mozilla/project_haiku.iot/Bluetooth/HC-05-Bluetooth-Module/Communicate_Master_Slave/BL-Slave-Pair/BL-Slave-Pair.ino

/*
* Sketch: Arduino2Arduino_SLAVE_01
* By Martyn Currey
* 08.04.2016
* Written in Arduino IDE 1.6.5
*
* Receive commands through a serial connection and turn a LED on or OFF
* There is no error checking and this sketch receives only
* Commands should be contained within the start and end markers < and >
*
* D8 - software serial RX
* D9 - software serial TX
* D3 - LED
*
*/
 
// AltSoftSerial uses D9 for TX and D8 for RX. While using AltSoftSerial D10 cannot be used for PWM.
// Remember to use a voltage divider on the Arduino TX pin / Bluetooth RX pin
// Download AltSoftSerial from https://www.pjrc.com/teensy/td_libs_AltSoftSerial.html
 
#include <AltSoftSerial.h>
AltSoftSerial BTserial; 
 
// Change DEBUG to true to output debug information to the serial monitor
boolean DEBUG = true;
 
 
// Variables used for incoming data
const byte maxDataLength = 20;          // maxDataLength is the maximum length allowed for received data.
char receivedChars[maxDataLength+1] ;
boolean newData = false;               // newData is used to determine if there is a new command
 
void setup()  
{
    // LED on pin 3
    pinMode(3, OUTPUT); 
    digitalWrite(3,LOW);
 
 
    if (DEBUG)
    {
        // open serial communication for debugging and show the sketch name and the date compiled
        Serial.begin(9600);
        Serial.println(__FILE__);
        Serial.println(__DATE__);
        Serial.println(" ");
    }
 
    //  open software serial connection to the Bluetooth module.
    BTserial.begin(9600); 
    if (DEBUG)  {   Serial.println(F("AltSoftSerial started at 9600"));     }
 
    newData = false;
 
}
 
void loop()  
{
         recvWithStartEndMarkers();                // check to see if we have received any new commands
         if (newData)  {   processCommand();  }    // if we have a new command do something
}
 
 
void processCommand()
{
    newData = false;
    if (DEBUG)  {   Serial.print("recieved data = ");  Serial.println(receivedChars);         }
 
    if      (strcmp ("LEDON",receivedChars) == 0)  { digitalWrite(3,HIGH);   }
    else if (strcmp ("LEDOFF",receivedChars) == 0) { digitalWrite(3,LOW);    }
}
 
// function recvWithStartEndMarkers by Robin2 of the Arduino forums
// See  http://forum.arduino.cc/index.php?topic=288234.0
void recvWithStartEndMarkers() 
{
     static boolean recvInProgress = false;
     static byte ndx = 0;
     char startMarker = '<';
     char endMarker = '>';
 
     if (BTserial.available() > 0) 
     {
          char rc = BTserial.read();
          if (recvInProgress == true) 
          {
               if (rc != endMarker) 
               {
                    if (ndx < maxDataLength) { receivedChars[ndx] = rc; ndx++;  }
               }
               else 
               {
                     receivedChars[ndx] = '\0'; // terminate the string
                     recvInProgress = false;
                     ndx = 0;
                     newData = true;
               }
          }
          else if (rc == startMarker) { recvInProgress = true; }
     }
 
}
