mozilla/project_haiku.iot/Bluetooth/HC-05-Bluetooth-Module/Setup_Master_Slave/BL-Master-Pair-SoftwareSerial-AT-Mode/BL-Master-Pair-SoftwareSerial-AT-Mode.ino

// Basic Bluetooth sketch HC-05_02_38400
// Connect the HC-05 module and communicate using the serial monitor
//
// The HC-05 defaults to commincation mode when first powered on.
// Needs to be placed in to AT mode
// After a factory reset the default baud rate for communication mode is 38400
//
//
//  Pins
//  BT VCC to Arduino 5V out. 
//  BT GND to GND
//  BT RX to Arduino pin 3 (through a voltage divider)
//  BT TX to Arduino pin 2 (no need voltage divider)
 
 
#include <SoftwareSerial.h>
SoftwareSerial BTserial(2, 3); // RX | TX
// Connect the HC-05 TX to Arduino pin 2 RX. 
// Connect the HC-05 RX to Arduino pin 3 TX through a voltage divider.
 
char c = ' ';
byte ATmodePin=4;
 
void setup() 
{

    // Set up the pin used to turn on AT mode
    // For full atmode connect pin34 to D4 Ardunio
    // Comment the below two lines to run bluetooth module
    // in communication/data mode
    pinMode(ATmodePin, OUTPUT); 
    digitalWrite(ATmodePin, HIGH); 
    
    // start th serial communication with the host computer
    Serial.begin(9600);
    Serial.println("Arduino with HC-05 is ready");
 
    /* Start communication with the HC-05 using 38400
     * Set it to 38400 for pair link and bind commands
     * AT+RNAME? 2016,1,69779
     * AT+PAIR=2016,1,69779,9
     * AT+BIND=2016,1,69779
     * AT+CMODE=1
     * AT+LINK=2016,1,69779
    */
    BTserial.begin(38400);  
    Serial.println("BTserial started at 38400");
}

void loop()
{
     // Keep reading from HC-05 and send to Arduino Serial Monitor
    if (BTserial.available())
    {  
        c = BTserial.read();
        Serial.write(c);
    }
 
    // Keep reading from Arduino Serial Monitor and send to HC-05
    if (Serial.available())
    {
        c =  Serial.read();
 
        // mirror the commands back to the serial monitor
        // makes it easy to follow the commands
        Serial.write(c);   
        BTserial.write(c);  
    }
 
}
