mozilla/project_haiku.iot/Prototype/UR2/InternetButton/buzzy-pixel/BlingButton.cpp

#include "BlingButton.h"
#include "math.h"

//----------------- Button ----------------//

uint8_t pixel_pin = 3;
uint8_t b1 = 4;
uint8_t vibe_pin = D5;
uint8_t battery_sense_pin = A5;

Adafruit_NeoPixel ring = Adafruit_NeoPixel(PIXEL_COUNT, pixel_pin, PIXEL_TYPE);
OneButton button = OneButton(b1, true);

BlingButton::BlingButton(){

}

void BlingButton::begin(){
    ring.begin();
    ring.show();

    pinMode(vibe_pin, OUTPUT);
    pinMode(b1, INPUT_PULLUP);
    String msg = "BlingButton begin";
    log(msg);

}

void BlingButton::log(String str){
  Particle.publish(BLINGBTN_LOGGING_TOPIC, str, 60, PRIVATE);
}

float BlingButton::batteryLevel() {
  const float voltsPerBit = 3.3 / 4095; // Calculate volts per bit of ADC reading
  const float ratioV = (47000 + 33000) / 33000; //Calculates to 4.636363
  int Vin = analogRead(battery_sense_pin);
  float rawVolts = Vin * voltsPerBit;  //Calculate voltage at A5 input
  float batteryVolts = rawVolts * ratioV;
  Serial.print("Voltage ");
  Serial.print(batteryVolts);
  Serial.print("Raw ");
  Serial.print (Vin);
  char batteryRaw[60];
  sprintf(batteryRaw, "%5.2f", rawVolts);
  log(batteryRaw);
  return batteryVolts;
};

void BlingButton::ledOn(uint8_t i, uint8_t r, uint8_t g, uint8_t b){
    //i-1 shifts the location from human readable to the right index for the LEDs
    if(i == 12){
        ring.setPixelColor(0, ring.Color(r,g,b));
        ring.setPixelColor(10, ring.Color(r,g,b));
    }
    else{
        ring.setPixelColor(i-1, ring.Color(r,g,b));
    }
    ring.show();
}

void BlingButton::ledOff(uint8_t i){
    ledOn(i,0,0,0);
}

void BlingButton::allLedsOff(){
    for(int i = 0; i<PIXEL_COUNT; i++){
            ring.setPixelColor(i, ring.Color(0, 0, 0));
    }
    ring.show();
}

void BlingButton::allLedsOn(uint8_t r, uint8_t g, uint8_t b){
    for(int i = 0; i<PIXEL_COUNT; i++){
            ring.setPixelColor(i, ring.Color(r, g, b));
    }
    ring.show();
}

uint8_t BlingButton::buttonOn(){
  return !digitalRead(b1);
}

void BlingButton::rainbow(uint8_t wait) {
  uint16_t i, j;

  for(j=0; j<256; j++) { // 1 cycle of all colors on wheel
    for(i=0; i< PIXEL_COUNT; i++) {
      uint8_t WheelPos = ((i * 256 / PIXEL_COUNT) + j) & 255;
      if(WheelPos < 85) {
         ring.setPixelColor(i,ring.Color(WheelPos * 3, 255 - WheelPos * 3, 0));
      } else if(WheelPos < 170) {
         WheelPos -= 85;
         ring.setPixelColor(i,ring.Color(255 - WheelPos * 3, 0, WheelPos * 3));
      } else {
         WheelPos -= 170;
         ring.setPixelColor(i,ring.Color(0, WheelPos * 3, 255 - WheelPos * 3));
      }
    }
    ring.show();
    delay(wait);
  }
}

// Fill the Neopixel one after the other with two colors
void BlingButton::dualColor(uint8_t r1, uint8_t g1, uint8_t b1,
  uint8_t r2, uint8_t g2, uint8_t b2, uint8_t wait) {
  uint32_t c = ring.Color(r1, g1, b1);
  uint32_t c1 = ring.Color(r2, g2, b2);
  for(uint16_t i=0; i<PIXEL_COUNT;i=i+2) {
    ring.setPixelColor(i, c);
    ring.setPixelColor(i+1, c1);
    ring.show();
    delay(wait);
  }
}

void BlingButton::vibrate(int duration){
    digitalWrite(vibe_pin, HIGH);
    delay(duration);
    digitalWrite(vibe_pin, LOW);
}

void BlingButton::attachClick(callbackFunction newFunction){
  button.attachClick(newFunction);
}

void BlingButton::attachDoubleClick(callbackFunction newFunction){
  button.attachDoubleClick(newFunction);
}

void BlingButton::attachLongPress(callbackFunction newFunction){
  button.attachLongPressStop(newFunction);
}

void BlingButton::listen(void){
  button.tick();
}

// ----------Button Handling----------------------//
// -----
// OneButton.cpp - Library for detecting button clicks, doubleclicks and long press pattern on a single button.
// This class is implemented for use with the Arduino environment.
// Copyright (c) by Matthias Hertel, http://www.mathertel.de
// This work is licensed under a BSD style license. See http://www.mathertel.de/License.aspx
// More information on: http://www.mathertel.de/Arduino
// -----
// An Arduino library for using a single button for multiple purpose input.
// https://github.com/mathertel/OneButton

// ----- Initialization and Default Values -----

OneButton::OneButton(int pin, int activeLow)
{
  pinMode(pin, INPUT);      // sets the MenuPin as input
  _pin = pin;

  _clickTicks = 600;        // number of millisec that have to pass by before a click is detected.
  _pressTicks = 1000;       // number of millisec that have to pass by before a long button press is detected.

  _state = 0; // starting with state 0: waiting for button to be pressed
  _isLongPressed = false;  // Keep track of long press state

  if (activeLow) {
    // button connects ground to the pin when pressed.
    _buttonReleased = HIGH; // notPressed
    _buttonPressed = LOW;
    digitalWrite(pin, HIGH);   // turn on pullUp resistor

  } else {
    // button connects VCC to the pin when pressed.
    _buttonReleased = LOW;
    _buttonPressed = HIGH;
  } // if


  _doubleClickFunc = NULL;
  _pressFunc = NULL;
  _longPressStartFunc = NULL;
  _longPressStopFunc = NULL;
  _duringLongPressFunc = NULL;
} // OneButton


// explicitly set the number of millisec that have to pass by before a click is detected.
void OneButton::setClickTicks(int ticks) {
  _clickTicks = ticks;
} // setClickTicks


// explicitly set the number of millisec that have to pass by before a long button press is detected.
void OneButton::setPressTicks(int ticks) {
  _pressTicks = ticks;
} // setPressTicks


// save function for click event
void OneButton::attachClick(callbackFunction newFunction)
{
  _clickFunc = newFunction;
} // attachClick


// save function for doubleClick event
void OneButton::attachDoubleClick(callbackFunction newFunction)
{
  _doubleClickFunc = newFunction;
} // attachDoubleClick


// save function for press event
// DEPRECATED, is replaced by attachLongPressStart, attachLongPressStop, attachDuringLongPress,
void OneButton::attachPress(callbackFunction newFunction)
{
  _pressFunc = newFunction;
} // attachPress

// save function for longPressStart event
void OneButton::attachLongPressStart(callbackFunction newFunction)
{
  _longPressStartFunc = newFunction;
} // attachLongPressStart

// save function for longPressStop event
void OneButton::attachLongPressStop(callbackFunction newFunction)
{
  _longPressStopFunc = newFunction;
} // attachLongPressStop

// save function for during longPress event
void OneButton::attachDuringLongPress(callbackFunction newFunction)
{
  _duringLongPressFunc = newFunction;
} // attachDuringLongPress

// function to get the current long pressed state
bool OneButton::isLongPressed(){
  return _isLongPressed;
}

void OneButton::tick(void)
{
  // Detect the input information
  int buttonLevel = digitalRead(_pin); // current button signal.
  unsigned long now = millis(); // current (relative) time in msecs.

  // Implementation of the state machine
  if (_state == 0) { // waiting for menu pin being pressed.
    if (buttonLevel == _buttonPressed) {
      _state = 1; // step to state 1
      _startTime = now; // remember starting time
    } // if

  } else if (_state == 1) { // waiting for menu pin being released.

    if ((buttonLevel == _buttonReleased) && ((unsigned long)(now - _startTime) < _debounceTicks)) {
      // button was released to quickly so I assume some debouncing.
	  // go back to state 0 without calling a function.
      _state = 0;

    } else if (buttonLevel == _buttonReleased) {
      _state = 2; // step to state 2

    } else if ((buttonLevel == _buttonPressed) && ((unsigned long)(now - _startTime) > _pressTicks)) {
      _isLongPressed = true;  // Keep track of long press state
      if (_pressFunc) _pressFunc();
	  if (_longPressStartFunc) _longPressStartFunc();
	  if (_duringLongPressFunc) _duringLongPressFunc();
      _state = 6; // step to state 6

    } else {
      // wait. Stay in this state.
    } // if

  } else if (_state == 2) { // waiting for menu pin being pressed the second time or timeout.
    if ((unsigned long)(now - _startTime) > _clickTicks) {
      // this was only a single short click
      if (_clickFunc) _clickFunc();
      _state = 0; // restart.

    } else if (buttonLevel == _buttonPressed) {
      _state = 3; // step to state 3
    } // if

  } else if (_state == 3) { // waiting for menu pin being released finally.
    if (buttonLevel == _buttonReleased) {
      // this was a 2 click sequence.
      if (_doubleClickFunc) _doubleClickFunc();
      _state = 0; // restart.
    } // if

  } else if (_state == 6) { // waiting for menu pin being release after long press.
    if (buttonLevel == _buttonReleased) {
	  _isLongPressed = false;  // Keep track of long press state
	  if(_longPressStopFunc) _longPressStopFunc();
      _state = 0; // restart.
    } else {
	  // button is being long pressed
	  _isLongPressed = true; // Keep track of long press state
	  if (_duringLongPressFunc) _duringLongPressFunc();
    } // if

  } // if
} // OneButton.tick()


//----------------- LED Handling ------------------------//

/*-------------------------------------------------------------------------
  Spark Core library to control WS2811/WS2812 based RGB
  LED devices such as Adafruit NeoPixel strips.
  Currently handles 800 KHz and 400kHz bitstream on Spark Core,
  WS2812, WS2812B and WS2811.

  Also supports Radio Shack Tri-Color Strip with TM1803 controller
  400kHz bitstream.

  Written by Phil Burgess / Paint Your Dragon for Adafruit Industries.
  Modified to work with Spark Core by Technobly.
  Modified to work with Spark Button by jenesaisdiq.
  Contributions by PJRC and other members of the open source community.

  Adafruit invests time and resources providing this open source code,
  please support Adafruit and open-source hardware by purchasing products
  from Adafruit!
  --------------------------------------------------------------------*/

/* ======================= Adafruit_NeoPixel.cpp ======================= */
/*-------------------------------------------------------------------------
  This file is part of the Adafruit NeoPixel library.
  https://github.com/adafruit/Adafruit_NeoPixel

  NeoPixel is free software: you can redistribute it and/or modify
  it under the terms of the GNU Lesser General Public License as
  published by the Free Software Foundation, either version 3 of
  the License, or (at your option) any later version.

  NeoPixel is distributed in the hope that it will be useful,
  but WITHOUT ANY WARRANTY; without even the implied warranty of
  MERCHANTABILITY or FITNESS FOR A PARTICULAR PURPOSE.  See the
  GNU Lesser General Public License for more details.

  You should have received a copy of the GNU Lesser General Public
  License along with NeoPixel.  If not, see
  <http://www.gnu.org/licenses/>.
  -------------------------------------------------------------------------*/

#if PLATFORM_ID == 0 // Core
  #define pinLO(_pin) (PIN_MAP[_pin].gpio_peripheral->BRR = PIN_MAP[_pin].gpio_pin)
  #define pinHI(_pin) (PIN_MAP[_pin].gpio_peripheral->BSRR = PIN_MAP[_pin].gpio_pin)
#elif PLATFORM_ID == 6 // Photon
  //#include "pinmap_impl.h"
  STM32_Pin_Info* PIN_MAP2 = HAL_Pin_Map(); // Pointer required for highest access speed
  #define pinLO(_pin) (PIN_MAP2[_pin].gpio_peripheral->BSRRH = PIN_MAP2[_pin].gpio_pin)
  #define pinHI(_pin) (PIN_MAP2[_pin].gpio_peripheral->BSRRL = PIN_MAP2[_pin].gpio_pin)
#else
  #error "*** PLATFORM_ID not supported by this library. PLATFORM should be Core or Photon ***"
#endif
// fast pin access
#define pinSet(_pin, _hilo) (_hilo ? pinHI(_pin) : pinLO(_pin))

Adafruit_NeoPixel::Adafruit_NeoPixel(uint16_t n, uint8_t p, uint8_t t) :
  numLEDs(n), numBytes(n*3), brightness(0), pixels(NULL), type(t), endTime(0)
{
  if((pixels = (uint8_t *)malloc(numBytes))) {
    memset(pixels, 0, numBytes);
  }
}

Adafruit_NeoPixel::~Adafruit_NeoPixel() {
  if(pixels) free(pixels);
  pinMode(pixel_pin, INPUT);
}

void Adafruit_NeoPixel::begin(void) {
  pinMode(pixel_pin, OUTPUT);
  digitalWrite(pixel_pin, LOW);
}

void Adafruit_NeoPixel::show(void) {
  if(!pixels) return;

  // Data latch = 24 or 50 microsecond pause in the output stream.  Rather than
  // put a delay at the end of the function, the ending time is noted and
  // the function will simply hold off (if needed) on issuing the
  // subsequent round of data until the latch time has elapsed.  This
  // allows the mainline code to start generating the next frame of data
  // rather than stalling for the latch.
  uint32_t wait_time; // wait time in microseconds.
  switch(type) {
    case TM1803: // TM1803 = 24us reset pulse
      wait_time = 24L;
      break;
    case TM1829: // TM1829 = 500us reset pulse
      wait_time = 500L;
      break;
    case WS2812B: // WS2812 & WS2812B = 50us reset pulse
    case WS2812B2:
    case WS2811: // WS2811 = 50us reset pulse
    default:     // default = 50us reset pulse
      wait_time = 50L;
      break;
  }
  while((micros() - endTime) < wait_time);
  // endTime is a private member (rather than global var) so that multiple
  // instances on different pins can be quickly issued in succession (each
  // instance doesn't delay the next).

  __disable_irq(); // Need 100% focus on instruction timing

  volatile uint32_t
    c,    // 24-bit pixel color
    mask; // 8-bit mask
  volatile uint16_t i = numBytes; // Output loop counter
  volatile uint8_t
    j,              // 8-bit inner loop counter
   *ptr = pixels,   // Pointer to next byte
    g,              // Current green byte value
    r,              // Current red byte value
    b;              // Current blue byte value

  if(type == WS2812B) { // same as WS2812, 800 KHz bitstream
    while(i) { // While bytes left... (3 bytes = 1 pixel)
      mask = 0x800000; // reset the mask
      i = i-3;      // decrement bytes remaining
      g = *ptr++;   // Next green byte value
      r = *ptr++;   // Next red byte value
      b = *ptr++;   // Next blue byte value
      c = ((uint32_t)g << 16) | ((uint32_t)r <<  8) | b; // Pack the next 3 bytes to keep timing tight
      j = 0;        // reset the 24-bit counter
      do {
        pinSet(pixel_pin, HIGH); // HIGH
        if (c & mask) { // if masked bit is high
          // WS2812 spec             700ns HIGH
          // Adafruit on Arduino    (meas. 812ns)
          // This lib on Spark Core (meas. 790ns)
          // This lib on Photon     (meas. 792ns)
          asm volatile(
            "mov r0, r0" "\n\t" "nop" "\n\t" "nop" "\n\t" "nop" "\n\t" "nop" "\n\t"
            "nop" "\n\t" "nop" "\n\t" "nop" "\n\t" "nop" "\n\t" "nop" "\n\t"
            "nop" "\n\t" "nop" "\n\t" "nop" "\n\t" "nop" "\n\t" "nop" "\n\t"
            "nop" "\n\t" "nop" "\n\t" "nop" "\n\t" "nop" "\n\t" "nop" "\n\t"
            "nop" "\n\t" "nop" "\n\t" "nop" "\n\t" "nop" "\n\t" "nop" "\n\t"
            "nop" "\n\t" "nop" "\n\t" "nop" "\n\t" "nop" "\n\t" "nop" "\n\t"
            "nop" "\n\t" "nop" "\n\t" "nop" "\n\t" "nop" "\n\t" "nop" "\n\t"
            "nop" "\n\t" "nop" "\n\t"
#if PLATFORM_ID == 6 // Photon
            "nop" "\n\t" "nop" "\n\t" "nop" "\n\t" "nop" "\n\t" "nop" "\n\t"
            "nop" "\n\t" "nop" "\n\t" "nop" "\n\t" "nop" "\n\t" "nop" "\n\t"
            "nop" "\n\t" "nop" "\n\t" "nop" "\n\t" "nop" "\n\t" "nop" "\n\t"
            "nop" "\n\t" "nop" "\n\t" "nop" "\n\t" "nop" "\n\t" "nop" "\n\t"
            "nop" "\n\t" "nop" "\n\t" "nop" "\n\t" "nop" "\n\t" "nop" "\n\t"
            "nop" "\n\t" "nop" "\n\t" "nop" "\n\t" "nop" "\n\t" "nop" "\n\t"
            "nop" "\n\t" "nop" "\n\t" "nop" "\n\t" "nop" "\n\t" "nop" "\n\t"
            "nop" "\n\t" "nop" "\n\t" "nop" "\n\t" "nop" "\n\t" "nop" "\n\t"
#endif
            ::: "r0", "cc", "memory");
          // WS2812 spec             600ns LOW
          // Adafruit on Arduino    (meas. 436ns)
          // This lib on Spark Core (meas. 445ns)
          // This lib on Photon     (meas. 434ns)
          pinSet(pixel_pin, LOW); // LOW
          asm volatile(
            "mov r0, r0" "\n\t"
#if PLATFORM_ID == 6 // Photon
            "nop" "\n\t" "nop" "\n\t" "nop" "\n\t" "nop" "\n\t" "nop" "\n\t"
            "nop" "\n\t" "nop" "\n\t" "nop" "\n\t" "nop" "\n\t" "nop" "\n\t"
            "nop" "\n\t" "nop" "\n\t" "nop" "\n\t" "nop" "\n\t" "nop" "\n\t"
            "nop" "\n\t" "nop" "\n\t" "nop" "\n\t" "nop" "\n\t" "nop" "\n\t"
            "nop" "\n\t" "nop" "\n\t" "nop" "\n\t" "nop" "\n\t" "nop" "\n\t"
            "nop" "\n\t" "nop" "\n\t"
#endif
            ::: "r0", "cc", "memory");
        }
        else { // else masked bit is low
          // WS2812 spec             350ns HIGH
          // Adafruit on Arduino    (meas. 312ns)
          // This lib on Spark Core (meas. 318ns)
          // This lib on Photon     (meas. 308ns)
          asm volatile(
            "mov r0, r0" "\n\t" "nop" "\n\t" "nop" "\n\t" "nop" "\n\t"
#if PLATFORM_ID == 6 // Photon
            "nop" "\n\t" "nop" "\n\t" "nop" "\n\t" "nop" "\n\t" "nop" "\n\t"
            "nop" "\n\t" "nop" "\n\t" "nop" "\n\t" "nop" "\n\t" "nop" "\n\t"
            "nop" "\n\t" "nop" "\n\t" "nop" "\n\t" "nop" "\n\t" "nop" "\n\t"
#endif
            ::: "r0", "cc", "memory");
          // WS2812 spec             800ns LOW
          // Adafruit on Arduino    (meas. 938ns)
          // This lib on Spark Core (meas. 946ns)
          // This lib on Photon     (meas. 934ns)
          pinSet(pixel_pin, LOW); // LOW
          asm volatile(
            "mov r0, r0" "\n\t" "nop" "\n\t" "nop" "\n\t" "nop" "\n\t" "nop" "\n\t"
            "nop" "\n\t" "nop" "\n\t" "nop" "\n\t" "nop" "\n\t" "nop" "\n\t"
            "nop" "\n\t" "nop" "\n\t" "nop" "\n\t" "nop" "\n\t" "nop" "\n\t"
            "nop" "\n\t" "nop" "\n\t" "nop" "\n\t" "nop" "\n\t" "nop" "\n\t"
            "nop" "\n\t" "nop" "\n\t" "nop" "\n\t" "nop" "\n\t" "nop" "\n\t"
            "nop" "\n\t" "nop" "\n\t" "nop" "\n\t" "nop" "\n\t" "nop" "\n\t"
            "nop" "\n\t" "nop" "\n\t" "nop" "\n\t"
#if PLATFORM_ID == 6 // Photon
            "nop" "\n\t" "nop" "\n\t" "nop" "\n\t" "nop" "\n\t" "nop" "\n\t"
            "nop" "\n\t" "nop" "\n\t" "nop" "\n\t" "nop" "\n\t" "nop" "\n\t"
            "nop" "\n\t" "nop" "\n\t" "nop" "\n\t" "nop" "\n\t" "nop" "\n\t"
            "nop" "\n\t" "nop" "\n\t" "nop" "\n\t" "nop" "\n\t" "nop" "\n\t"
            "nop" "\n\t" "nop" "\n\t" "nop" "\n\t" "nop" "\n\t" "nop" "\n\t"
            "nop" "\n\t" "nop" "\n\t" "nop" "\n\t" "nop" "\n\t" "nop" "\n\t"
            "nop" "\n\t" "nop" "\n\t" "nop" "\n\t" "nop" "\n\t" "nop" "\n\t"
            "nop" "\n\t" "nop" "\n\t" "nop" "\n\t" "nop" "\n\t" "nop" "\n\t"
            "nop" "\n\t" "nop" "\n\t" "nop" "\n\t" "nop" "\n\t" "nop" "\n\t"
            "nop" "\n\t" "nop" "\n\t" "nop" "\n\t" "nop" "\n\t" "nop" "\n\t"
            "nop" "\n\t" "nop" "\n\t"
#endif
            ::: "r0", "cc", "memory");
        }
        mask >>= 1;
      } while ( ++j < 24 ); // ... pixel done
    } // end while(i) ... no more pixels
  }
  else if(type == WS2812B2) { // WS2812B with DWT timer
#if PLATFORM_ID == 6 // Photon
    #define CYCLES_800_T0H  25 // 312ns (meas. 300ns)
    #define CYCLES_800_T0L  70 // 938ns (meas. 940ns)
    #define CYCLES_800_T1H  80 // 812ns (meas. 792ns)
    #define CYCLES_800_T1L  8  // 436ns (meas. 425ns)

    volatile uint32_t cyc;

    while(i) { // While bytes left... (3 bytes = 1 pixel)
      mask = 0x800000; // reset the mask
      i = i-3;      // decrement bytes remaining
      g = *ptr++;   // Next green byte value
      r = *ptr++;   // Next red byte value
      b = *ptr++;   // Next blue byte value
      c = ((uint32_t)g << 16) | ((uint32_t)r <<  8) | b; // Pack the next 3 bytes to keep timing tight
      j = 0;        // reset the 24-bit counter
      do {
        cyc = DWT->CYCCNT;
        pinSet(pixel_pin, HIGH); // HIGH
        if (c & mask) { // if masked bit is high
          while(DWT->CYCCNT - cyc < CYCLES_800_T1H);
          pinSet(pixel_pin, LOW);
          cyc = DWT->CYCCNT;
          while(DWT->CYCCNT - cyc < CYCLES_800_T1L);
        }
        else { // else masked bit is low
          while(DWT->CYCCNT - cyc < CYCLES_800_T0H);
          pinSet(pixel_pin, LOW);
          cyc = DWT->CYCCNT;
          while(DWT->CYCCNT - cyc < CYCLES_800_T0L);
        }
        mask >>= 1;
      } while ( ++j < 24 ); // ... pixel done
    } // end while(i) ... no more pixels
#endif
  }
  else if(type == WS2811) { // WS2811, 400 KHz bitstream
    while(i) { // While bytes left... (3 bytes = 1 pixel)
      mask = 0x800000; // reset the mask
      i = i-3;      // decrement bytes remaining
      r = *ptr++;   // Next red byte value
      g = *ptr++;   // Next green byte value
      b = *ptr++;   // Next blue byte value
      c = ((uint32_t)r << 16) | ((uint32_t)g <<  8) | b; // Pack the next 3 bytes to keep timing tight
      j = 0;        // reset the 24-bit counter
      do {
        pinSet(pixel_pin, HIGH); // HIGH
        if (c & mask) { // if masked bit is high
          // WS2811 spec             1.20us HIGH
          // Adafruit on Arduino    (meas. 1.25us)
          // This lib on Spark Core (meas. 1.25us)
          asm volatile(
            "mov r0, r0" "\n\t" "nop" "\n\t" "nop" "\n\t" "nop" "\n\t" "nop" "\n\t"
            "nop" "\n\t" "nop" "\n\t" "nop" "\n\t" "nop" "\n\t" "nop" "\n\t"
            "nop" "\n\t" "nop" "\n\t" "nop" "\n\t" "nop" "\n\t" "nop" "\n\t"
            "nop" "\n\t" "nop" "\n\t" "nop" "\n\t" "nop" "\n\t" "nop" "\n\t"
            "nop" "\n\t" "nop" "\n\t" "nop" "\n\t" "nop" "\n\t" "nop" "\n\t"
            "nop" "\n\t" "nop" "\n\t" "nop" "\n\t" "nop" "\n\t" "nop" "\n\t"
            "nop" "\n\t" "nop" "\n\t" "nop" "\n\t" "nop" "\n\t" "nop" "\n\t"
            "nop" "\n\t" "nop" "\n\t" "nop" "\n\t" "nop" "\n\t" "nop" "\n\t"
            "nop" "\n\t" "nop" "\n\t" "nop" "\n\t" "nop" "\n\t" "nop" "\n\t"
            "nop" "\n\t" "nop" "\n\t" "nop" "\n\t" "nop" "\n\t" "nop" "\n\t"
            "nop" "\n\t" "nop" "\n\t" "nop" "\n\t" "nop" "\n\t" "nop" "\n\t"
            "nop" "\n\t" "nop" "\n\t" "nop" "\n\t" "nop" "\n\t" "nop" "\n\t"
            "nop" "\n\t" "nop" "\n\t" "nop" "\n\t" "nop" "\n\t" "nop" "\n\t"
            "nop" "\n\t" "nop" "\n\t" "nop" "\n\t" "nop" "\n\t" "nop" "\n\t"
            ::: "r0", "cc", "memory");
          // WS2811 spec             1.30us LOW
          // Adafruit on Arduino    (meas. 1.25us)
          // This lib on Spark Core (meas. 1.24us)
          pinSet(pixel_pin, LOW); // LOW
          asm volatile(
            "mov r0, r0" "\n\t" "nop" "\n\t" "nop" "\n\t" "nop" "\n\t" "nop" "\n\t"
            "nop" "\n\t" "nop" "\n\t" "nop" "\n\t" "nop" "\n\t" "nop" "\n\t"
            "nop" "\n\t" "nop" "\n\t" "nop" "\n\t" "nop" "\n\t" "nop" "\n\t"
            "nop" "\n\t" "nop" "\n\t" "nop" "\n\t" "nop" "\n\t" "nop" "\n\t"
            "nop" "\n\t" "nop" "\n\t" "nop" "\n\t" "nop" "\n\t" "nop" "\n\t"
            "nop" "\n\t" "nop" "\n\t" "nop" "\n\t" "nop" "\n\t" "nop" "\n\t"
            "nop" "\n\t" "nop" "\n\t" "nop" "\n\t" "nop" "\n\t" "nop" "\n\t"
            "nop" "\n\t" "nop" "\n\t" "nop" "\n\t" "nop" "\n\t" "nop" "\n\t"
            "nop" "\n\t" "nop" "\n\t" "nop" "\n\t" "nop" "\n\t" "nop" "\n\t"
            "nop" "\n\t" "nop" "\n\t" "nop" "\n\t" "nop" "\n\t" "nop" "\n\t"
            "nop" "\n\t" "nop" "\n\t" "nop" "\n\t" "nop" "\n\t" "nop" "\n\t"
            "nop" "\n\t" "nop" "\n\t"
            ::: "r0", "cc", "memory");
        }
        else { // else masked bit is low
          // WS2811 spec             500ns HIGH
          // Adafruit on Arduino    (meas. 500ns)
          // This lib on Spark Core (meas. 500ns)
          asm volatile(
            "mov r0, r0" "\n\t" "nop" "\n\t" "nop" "\n\t" "nop" "\n\t" "nop" "\n\t"
            "nop" "\n\t" "nop" "\n\t" "nop" "\n\t" "nop" "\n\t" "nop" "\n\t"
            "nop" "\n\t" "nop" "\n\t" "nop" "\n\t" "nop" "\n\t" "nop" "\n\t"
            "nop" "\n\t" "nop" "\n\t"
            ::: "r0", "cc", "memory");
          // WS2811 spec             2.000us LOW
          // Adafruit on Arduino    (meas. 2.000us)
          // This lib on Spark Core (meas. 2.000us)
          pinSet(pixel_pin, LOW); // LOW
          asm volatile(
            "mov r0, r0" "\n\t" "nop" "\n\t" "nop" "\n\t" "nop" "\n\t" "nop" "\n\t"
            "nop" "\n\t" "nop" "\n\t" "nop" "\n\t" "nop" "\n\t" "nop" "\n\t"
            "nop" "\n\t" "nop" "\n\t" "nop" "\n\t" "nop" "\n\t" "nop" "\n\t"
            "nop" "\n\t" "nop" "\n\t" "nop" "\n\t" "nop" "\n\t" "nop" "\n\t"
            "nop" "\n\t" "nop" "\n\t" "nop" "\n\t" "nop" "\n\t" "nop" "\n\t"
            "nop" "\n\t" "nop" "\n\t" "nop" "\n\t" "nop" "\n\t" "nop" "\n\t"
            "nop" "\n\t" "nop" "\n\t" "nop" "\n\t" "nop" "\n\t" "nop" "\n\t"
            "nop" "\n\t" "nop" "\n\t" "nop" "\n\t" "nop" "\n\t" "nop" "\n\t"
            "nop" "\n\t" "nop" "\n\t" "nop" "\n\t" "nop" "\n\t" "nop" "\n\t"
            "nop" "\n\t" "nop" "\n\t" "nop" "\n\t" "nop" "\n\t" "nop" "\n\t"
            "nop" "\n\t" "nop" "\n\t" "nop" "\n\t" "nop" "\n\t" "nop" "\n\t"
            "nop" "\n\t" "nop" "\n\t" "nop" "\n\t" "nop" "\n\t" "nop" "\n\t"
            "nop" "\n\t" "nop" "\n\t" "nop" "\n\t" "nop" "\n\t" "nop" "\n\t"
            "nop" "\n\t" "nop" "\n\t" "nop" "\n\t" "nop" "\n\t" "nop" "\n\t"
            "nop" "\n\t" "nop" "\n\t" "nop" "\n\t" "nop" "\n\t" "nop" "\n\t"
            "nop" "\n\t" "nop" "\n\t" "nop" "\n\t" "nop" "\n\t" "nop" "\n\t"
            "nop" "\n\t" "nop" "\n\t" "nop" "\n\t" "nop" "\n\t" "nop" "\n\t"
            "nop" "\n\t" "nop" "\n\t" "nop" "\n\t" "nop" "\n\t" "nop" "\n\t"
            "nop" "\n\t" "nop" "\n\t" "nop" "\n\t" "nop" "\n\t" "nop" "\n\t"
            "nop" "\n\t" "nop" "\n\t" "nop" "\n\t" "nop" "\n\t" "nop" "\n\t"
            "nop" "\n\t" "nop" "\n\t" "nop" "\n\t" "nop" "\n\t" "nop" "\n\t"
            "nop" "\n\t" "nop" "\n\t" "nop" "\n\t"
            ::: "r0", "cc", "memory");
        }
        mask >>= 1;
      } while ( ++j < 24 ); // ... pixel done
    } // end while(i) ... no more pixels
  }
  else if(type == TM1803) { // TM1803 (Radio Shack Tri-Color Strip), 400 KHz bitstream
    while(i) { // While bytes left... (3 bytes = 1 pixel)
      mask = 0x800000; // reset the mask
      i = i-3;      // decrement bytes remaining
      r = *ptr++;   // Next red byte value
      g = *ptr++;   // Next blue byte value
      b = *ptr++;   // Next green byte value
      c = ((uint32_t)r << 16) | ((uint32_t)g <<  8) | b; // Pack the next 3 bytes to keep timing tight
      j = 0;        // reset the 24-bit counter
      do {
        pinSet(pixel_pin, HIGH); // HIGH
        if (c & mask) { // if masked bit is high
          // TM1803 spec             1.36us HIGH
          // Pololu on Arduino      (meas. 1.31us)
          // This lib on Spark Core (meas. 1.36us)
          asm volatile(
            "mov r0, r0" "\n\t" "nop" "\n\t" "nop" "\n\t" "nop" "\n\t" "nop" "\n\t"
            "nop" "\n\t" "nop" "\n\t" "nop" "\n\t" "nop" "\n\t" "nop" "\n\t"
            "nop" "\n\t" "nop" "\n\t" "nop" "\n\t" "nop" "\n\t" "nop" "\n\t"
            "nop" "\n\t" "nop" "\n\t" "nop" "\n\t" "nop" "\n\t" "nop" "\n\t"
            "nop" "\n\t" "nop" "\n\t" "nop" "\n\t" "nop" "\n\t" "nop" "\n\t"
            "nop" "\n\t" "nop" "\n\t" "nop" "\n\t" "nop" "\n\t" "nop" "\n\t"
            "nop" "\n\t" "nop" "\n\t" "nop" "\n\t" "nop" "\n\t" "nop" "\n\t"
            "nop" "\n\t" "nop" "\n\t" "nop" "\n\t" "nop" "\n\t" "nop" "\n\t"
            "nop" "\n\t" "nop" "\n\t" "nop" "\n\t" "nop" "\n\t" "nop" "\n\t"
            "nop" "\n\t" "nop" "\n\t" "nop" "\n\t" "nop" "\n\t" "nop" "\n\t"
            "nop" "\n\t" "nop" "\n\t" "nop" "\n\t" "nop" "\n\t" "nop" "\n\t"
            "nop" "\n\t" "nop" "\n\t" "nop" "\n\t" "nop" "\n\t" "nop" "\n\t"
            "nop" "\n\t" "nop" "\n\t" "nop" "\n\t" "nop" "\n\t" "nop" "\n\t"
            "nop" "\n\t" "nop" "\n\t" "nop" "\n\t" "nop" "\n\t" "nop" "\n\t"
            "nop" "\n\t" "nop" "\n\t" "nop" "\n\t" "nop" "\n\t" "nop" "\n\t"
            "nop" "\n\t" "nop" "\n\t" "nop" "\n\t" "nop" "\n\t"
            ::: "r0", "cc", "memory");
          // TM1803 spec             680ns LOW
          // Pololu on Arduino      (meas. 1.024us)
          // This lib on Spark Core (meas. 680ns)
          pinSet(pixel_pin, LOW); // LOW
          asm volatile(
            "mov r0, r0" "\n\t" "nop" "\n\t" "nop" "\n\t" "nop" "\n\t" "nop" "\n\t"
            "nop" "\n\t" "nop" "\n\t" "nop" "\n\t" "nop" "\n\t" "nop" "\n\t"
            "nop" "\n\t" "nop" "\n\t" "nop" "\n\t" "nop" "\n\t" "nop" "\n\t"
            ::: "r0", "cc", "memory");
        }
        else { // else masked bit is low
          // TM1803 spec             680ns HIGH
          // Pololu on Arduino      (meas. 374ns)
          // This lib on Spark Core (meas. 680ns)
          asm volatile(
            "mov r0, r0" "\n\t" "nop" "\n\t" "nop" "\n\t" "nop" "\n\t" "nop" "\n\t"
            "nop" "\n\t" "nop" "\n\t" "nop" "\n\t" "nop" "\n\t" "nop" "\n\t"
            "nop" "\n\t" "nop" "\n\t" "nop" "\n\t" "nop" "\n\t" "nop" "\n\t"
            "nop" "\n\t" "nop" "\n\t" "nop" "\n\t" "nop" "\n\t" "nop" "\n\t"
            "nop" "\n\t" "nop" "\n\t" "nop" "\n\t" "nop" "\n\t" "nop" "\n\t"
            "nop" "\n\t" "nop" "\n\t" "nop" "\n\t" "nop" "\n\t"
            ::: "r0", "cc", "memory");
          // TM1803 spec             1.36us LOW
          // Pololu on Arduino      (meas. 2.00us)
          // This lib on Spark Core (meas. 1.36us)
          pinSet(pixel_pin, LOW); // LOW
          asm volatile(
            "mov r0, r0" "\n\t" "nop" "\n\t" "nop" "\n\t" "nop" "\n\t" "nop" "\n\t"
            "nop" "\n\t" "nop" "\n\t" "nop" "\n\t" "nop" "\n\t" "nop" "\n\t"
            "nop" "\n\t" "nop" "\n\t" "nop" "\n\t" "nop" "\n\t" "nop" "\n\t"
            "nop" "\n\t" "nop" "\n\t" "nop" "\n\t" "nop" "\n\t" "nop" "\n\t"
            "nop" "\n\t" "nop" "\n\t" "nop" "\n\t" "nop" "\n\t" "nop" "\n\t"
            "nop" "\n\t" "nop" "\n\t" "nop" "\n\t" "nop" "\n\t" "nop" "\n\t"
            "nop" "\n\t" "nop" "\n\t" "nop" "\n\t" "nop" "\n\t" "nop" "\n\t"
            "nop" "\n\t" "nop" "\n\t" "nop" "\n\t" "nop" "\n\t" "nop" "\n\t"
            "nop" "\n\t" "nop" "\n\t" "nop" "\n\t" "nop" "\n\t" "nop" "\n\t"
            "nop" "\n\t" "nop" "\n\t" "nop" "\n\t" "nop" "\n\t" "nop" "\n\t"
            "nop" "\n\t" "nop" "\n\t" "nop" "\n\t" "nop" "\n\t" "nop" "\n\t"
            "nop" "\n\t" "nop" "\n\t" "nop" "\n\t" "nop" "\n\t" "nop" "\n\t"
            ::: "r0", "cc", "memory");
        }
        mask >>= 1;
      } while ( ++j < 24 ); // ... pixel done
    } // end while(i) ... no more pixels
  }
  else { // must be only other option TM1829, 800 KHz bitstream
    while(i) { // While bytes left... (3 bytes = 1 pixel)
      mask = 0x800000; // reset the mask
      i = i-3;      // decrement bytes remaining
      r = *ptr++;   // Next red byte value
      b = *ptr++;   // Next blue byte value
      g = *ptr++;   // Next green byte value
      c = ((uint32_t)r << 16) | ((uint32_t)b <<  8) | g; // Pack the next 3 bytes to keep timing tight
      j = 0;        // reset the 24-bit counter
      pinSet(pixel_pin, LOW); // LOW
      for( ;; ) {   // ... pixel done
        if (c & mask) { // if masked bit is high
          // TM1829 spec             800ns LOW
          // This lib on Spark Core (meas. 792ns)
          mask >>= 1; // Do this task during the long delay of this bit
          asm volatile(
            "mov r0, r0" "\n\t" "nop" "\n\t" "nop" "\n\t" "nop" "\n\t" "nop" "\n\t"
            "nop" "\n\t" "nop" "\n\t" "nop" "\n\t" "nop" "\n\t" "nop" "\n\t"
            "nop" "\n\t" "nop" "\n\t" "nop" "\n\t" "nop" "\n\t" "nop" "\n\t"
            "nop" "\n\t" "nop" "\n\t" "nop" "\n\t" "nop" "\n\t" "nop" "\n\t"
            "nop" "\n\t" "nop" "\n\t" "nop" "\n\t" "nop" "\n\t" "nop" "\n\t"
            ::: "r0", "cc", "memory");
          j++;
          // TM1829 spec             300ns HIGH
          // This lib on Spark Core (meas. 319ns)
          pinSet(pixel_pin, HIGH); // HIGH
          asm volatile(
            "mov r0, r0" "\n\t" "nop" "\n\t"
            ::: "r0", "cc", "memory");
          if(j==24) break;
          pinSet(pixel_pin, LOW); // LOW
        }
        else { // else masked bit is low
          // TM1829 spec             300ns LOW
          // This lib on Spark Core (meas. 306ns)
          asm volatile(
            "mov r0, r0" "\n\t" "nop" "\n\t" "nop" "\n\t" "nop" "\n\t"
            ::: "r0", "cc", "memory");
          // TM1829 spec             800ns HIGH
          // This lib on Spark Core (meas. 805ns)
          pinSet(pixel_pin, HIGH); // HIGH
          j++;
          mask >>= 1; // Do this task during the long delay of this bit
          asm volatile(
            "mov r0, r0" "\n\t" "nop" "\n\t" "nop" "\n\t" "nop" "\n\t" "nop" "\n\t"
            "nop" "\n\t" "nop" "\n\t" "nop" "\n\t" "nop" "\n\t" "nop" "\n\t"
            "nop" "\n\t" "nop" "\n\t" "nop" "\n\t" "nop" "\n\t" "nop" "\n\t"
            "nop" "\n\t" "nop" "\n\t" "nop" "\n\t" "nop" "\n\t" "nop" "\n\t"
            "nop" "\n\t" "nop" "\n\t" "nop" "\n\t" "nop" "\n\t" "nop" "\n\t"
            "nop" "\n\t" "nop" "\n\t" "nop" "\n\t" "nop" "\n\t"
            ::: "r0", "cc", "memory");
          if(j==24) break;
          pinSet(pixel_pin, LOW); // LOW
        }
      }
    } // end while(i) ... no more pixels
  }

  __enable_irq();
  endTime = micros(); // Save EOD time for latch on next call
}

// Set the output pin number
void Adafruit_NeoPixel::setPin(uint8_t p) {
  pinMode(pixel_pin, INPUT);
  pixel_pin = p;
  pinMode(p, OUTPUT);
  digitalWrite(p, LOW);
}

// Set pixel color from separate R,G,B components:
void Adafruit_NeoPixel::setPixelColor(
 uint16_t n, uint8_t r, uint8_t g, uint8_t b) {
  if(n < numLEDs) {
    if(brightness) { // See notes in setBrightness()
      r = (r * brightness) >> 8;
      g = (g * brightness) >> 8;
      b = (b * brightness) >> 8;
    }
    uint8_t *p = &pixels[n * 3];
    switch(type) {
      case WS2812B: // WS2812 & WS2812B is GRB order.
      case WS2812B2:
        *p++ = g;
        *p++ = r;
        *p = b;
        break;
      case TM1829: // TM1829 is special RBG order
        if(r == 255) r = 254; // 255 on RED channel causes display to be in a special mode.
        *p++ = r;
        *p++ = b;
        *p = g;
        break;
      case WS2811: // WS2811 is RGB order
      case TM1803: // TM1803 is RGB order
      default:     // default is RGB order
        *p++ = r;
        *p++ = g;
        *p = b;
        break;
    }
  }
}

// Set pixel color from 'packed' 32-bit RGB color:
void Adafruit_NeoPixel::setPixelColor(uint16_t n, uint32_t c) {
  if(n < numLEDs) {
    uint8_t
      r = (uint8_t)(c >> 16),
      g = (uint8_t)(c >>  8),
      b = (uint8_t)c;
    if(brightness) { // See notes in setBrightness()
      r = (r * brightness) >> 8;
      g = (g * brightness) >> 8;
      b = (b * brightness) >> 8;
    }
    uint8_t *p = &pixels[n * 3];
    switch(type) {
      case WS2812B: // WS2812 & WS2812B is GRB order.
      case WS2812B2:
        *p++ = g;
        *p++ = r;
        *p = b;
        break;
      case TM1829: // TM1829 is special RBG order
        if(r == 255) r = 254; // 255 on RED channel causes display to be in a special mode.
        *p++ = r;
        *p++ = b;
        *p = g;
        break;
      case WS2811: // WS2811 is RGB order
      case TM1803: // TM1803 is RGB order
      default:     // default is RGB order
        *p++ = r;
        *p++ = g;
        *p = b;
        break;
    }
  }
}

// Convert separate R,G,B into packed 32-bit RGB color.
// Packed format is always RGB, regardless of LED strand color order.
uint32_t Adafruit_NeoPixel::Color(uint8_t r, uint8_t g, uint8_t b) {
  return ((uint32_t)r << 16) | ((uint32_t)g <<  8) | b;
}

// Query color from previously-set pixel (returns packed 32-bit RGB value)
uint32_t Adafruit_NeoPixel::getPixelColor(uint16_t n) const {
  if(n >= numLEDs) {
    // Out of bounds, return no color.
    return 0;
  }
  uint8_t *p = &pixels[n * 3];
  uint32_t c;

  switch(type) {
    case WS2812B: // WS2812 & WS2812B is GRB order.
    case WS2812B2:
      c = ((uint32_t)p[1] << 16) | ((uint32_t)p[0] <<  8) | (uint32_t)p[2];
      break;
    case TM1829: // TM1829 is special RBG order
      c = ((uint32_t)p[0] << 16) | ((uint32_t)p[2] <<  8) | (uint32_t)p[1];
      break;
    case WS2811: // WS2811 is RGB order
    case TM1803: // TM1803 is RGB order
    default:     // default is RGB order
      c = ((uint32_t)p[0] << 16) | ((uint32_t)p[1] <<  8) | (uint32_t)p[2];
      break;
  }

  // Adjust this back up to the true color, as setting a pixel color will
  // scale it back down again.
  if(brightness) { // See notes in setBrightness()
    //Cast the color to a byte array
    uint8_t * c_ptr =reinterpret_cast<uint8_t*>(&c);
    c_ptr[0] = (c_ptr[0] << 8)/brightness;
    c_ptr[1] = (c_ptr[1] << 8)/brightness;
    c_ptr[2] = (c_ptr[2] << 8)/brightness;
  }
  return c; // Pixel # is out of bounds
}

uint8_t *Adafruit_NeoPixel::getPixels(void) const {
  return pixels;
}

uint16_t Adafruit_NeoPixel::numPixels(void) const {
  return numLEDs;
}

// Adjust output brightness; 0=darkest (off), 255=brightest.  This does
// NOT immediately affect what's currently displayed on the LEDs.  The
// next call to show() will refresh the LEDs at this level.  However,
// this process is potentially "lossy," especially when increasing
// brightness.  The tight timing in the WS2811/WS2812 code means there
// aren't enough free cycles to perform this scaling on the fly as data
// is issued.  So we make a pass through the existing color data in RAM
// and scale it (subsequent graphics commands also work at this
// brightness level).  If there's a significant step up in brightness,
// the limited number of steps (quantization) in the old data will be
// quite visible in the re-scaled version.  For a non-destructive
// change, you'll need to re-render the full strip data.  C'est la vie.
void Adafruit_NeoPixel::setBrightness(uint8_t b) {
  // Stored brightness value is different than what's passed.
  // This simplifies the actual scaling math later, allowing a fast
  // 8x8-bit multiply and taking the MSB.  'brightness' is a uint8_t,
  // adding 1 here may (intentionally) roll over...so 0 = max brightness
  // (color values are interpreted literally; no scaling), 1 = min
  // brightness (off), 255 = just below max brightness.
  uint8_t newBrightness = b + 1;
  if(newBrightness != brightness) { // Compare against prior value
    // Brightness has changed -- re-scale existing data in RAM
    uint8_t  c,
            *ptr           = pixels,
             oldBrightness = brightness - 1; // De-wrap old brightness value
    uint16_t scale;
    if(oldBrightness == 0) scale = 0; // Avoid /0
    else if(b == 255) scale = 65535 / oldBrightness;
    else scale = (((uint16_t)newBrightness << 8) - 1) / oldBrightness;
    for(uint16_t i=0; i<numBytes; i++) {
      c      = *ptr;
      *ptr++ = (c * scale) >> 8;
    }
    brightness = newBrightness;
  }
}

//Return the brightness value
uint8_t Adafruit_NeoPixel::getBrightness(void) const {
  return brightness - 1;
}

void Adafruit_NeoPixel::clear(void) {
  memset(pixels, 0, numBytes);
}
